scottlawsonbc/FilamentDiameterSensor/code/EdgeFinder/coordinate-reference.png

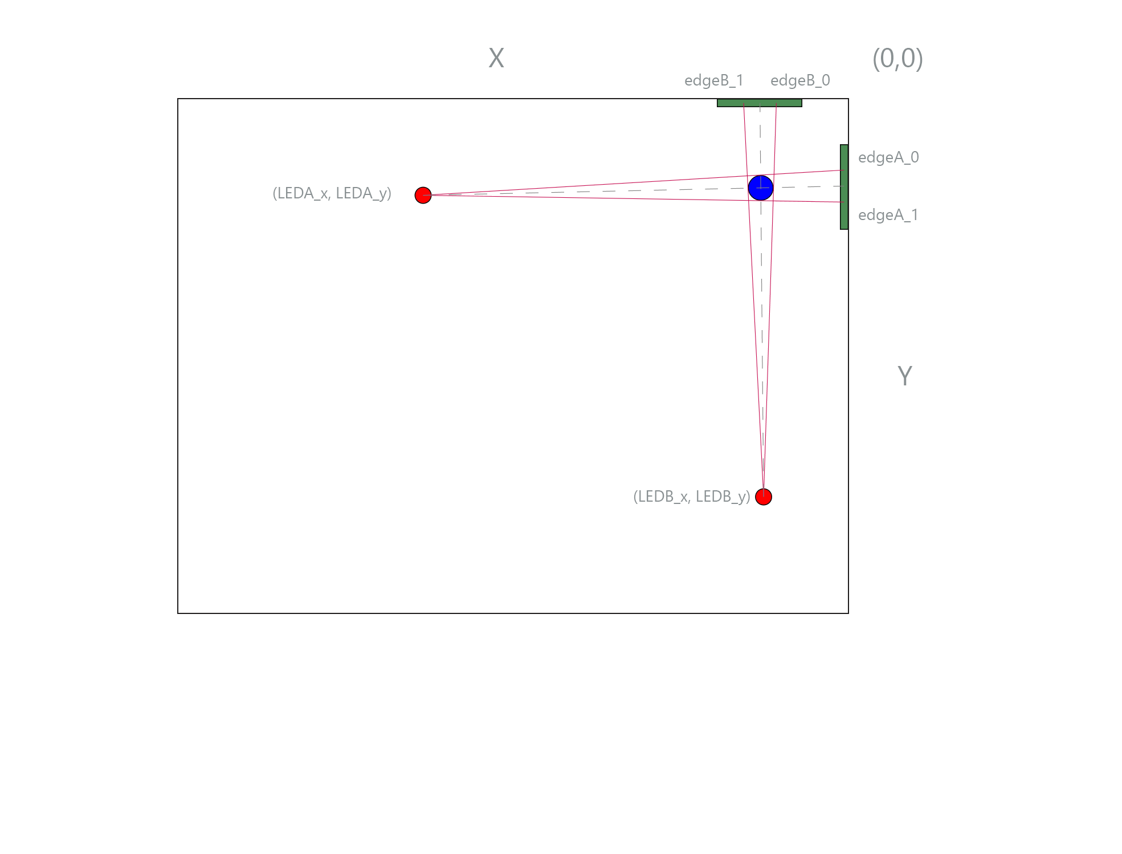
code/EdgeFinder/coordinate-reference.png
