scottlawsonbc/FilamentDiameterSensor/pictures/simulator.png

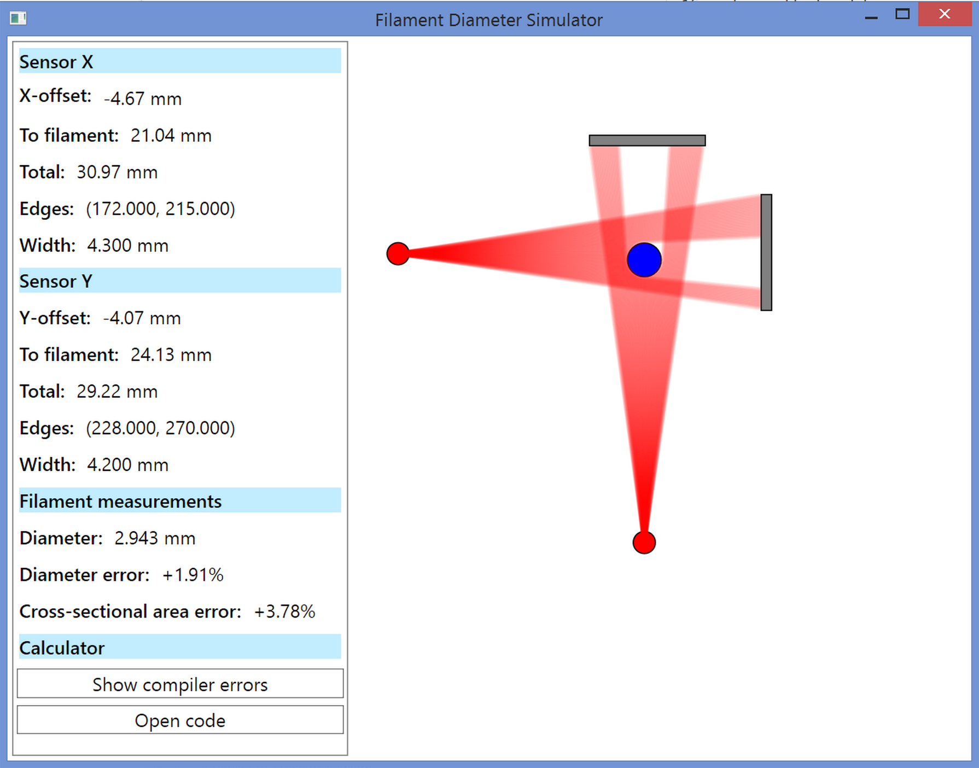
pictures/simulator.png
