scottlawsonbc/FilamentDiameterSensor/pictures/under-extrusion-example.jpg

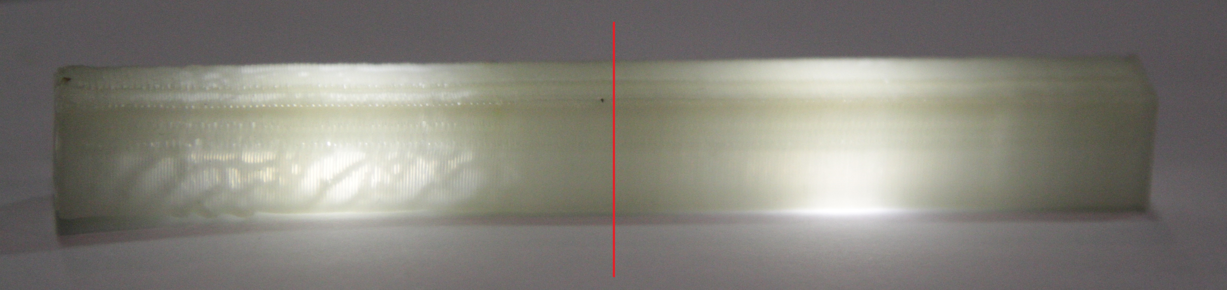
pictures/under-extrusion-example.jpg
