scottlawsonbc/FilamentDiameterSensor/reference-documents/stm32f3/adc-block-diagram.png

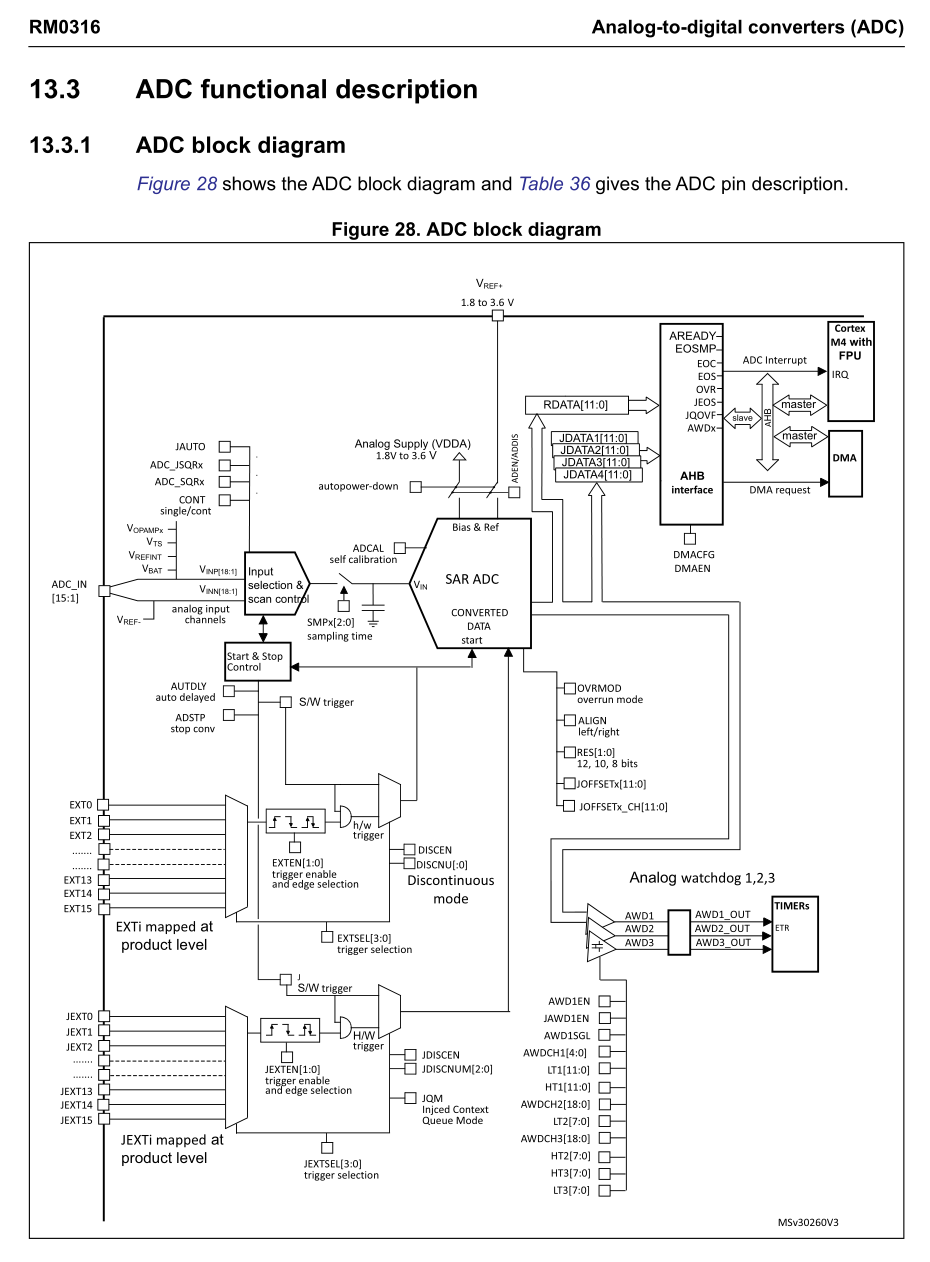
reference-documents/stm32f3/adc-block-diagram.png
