scottlawsonbc/FilamentDiameterSensor/reference-documents/stm32f3/adc-channel-mapping.png

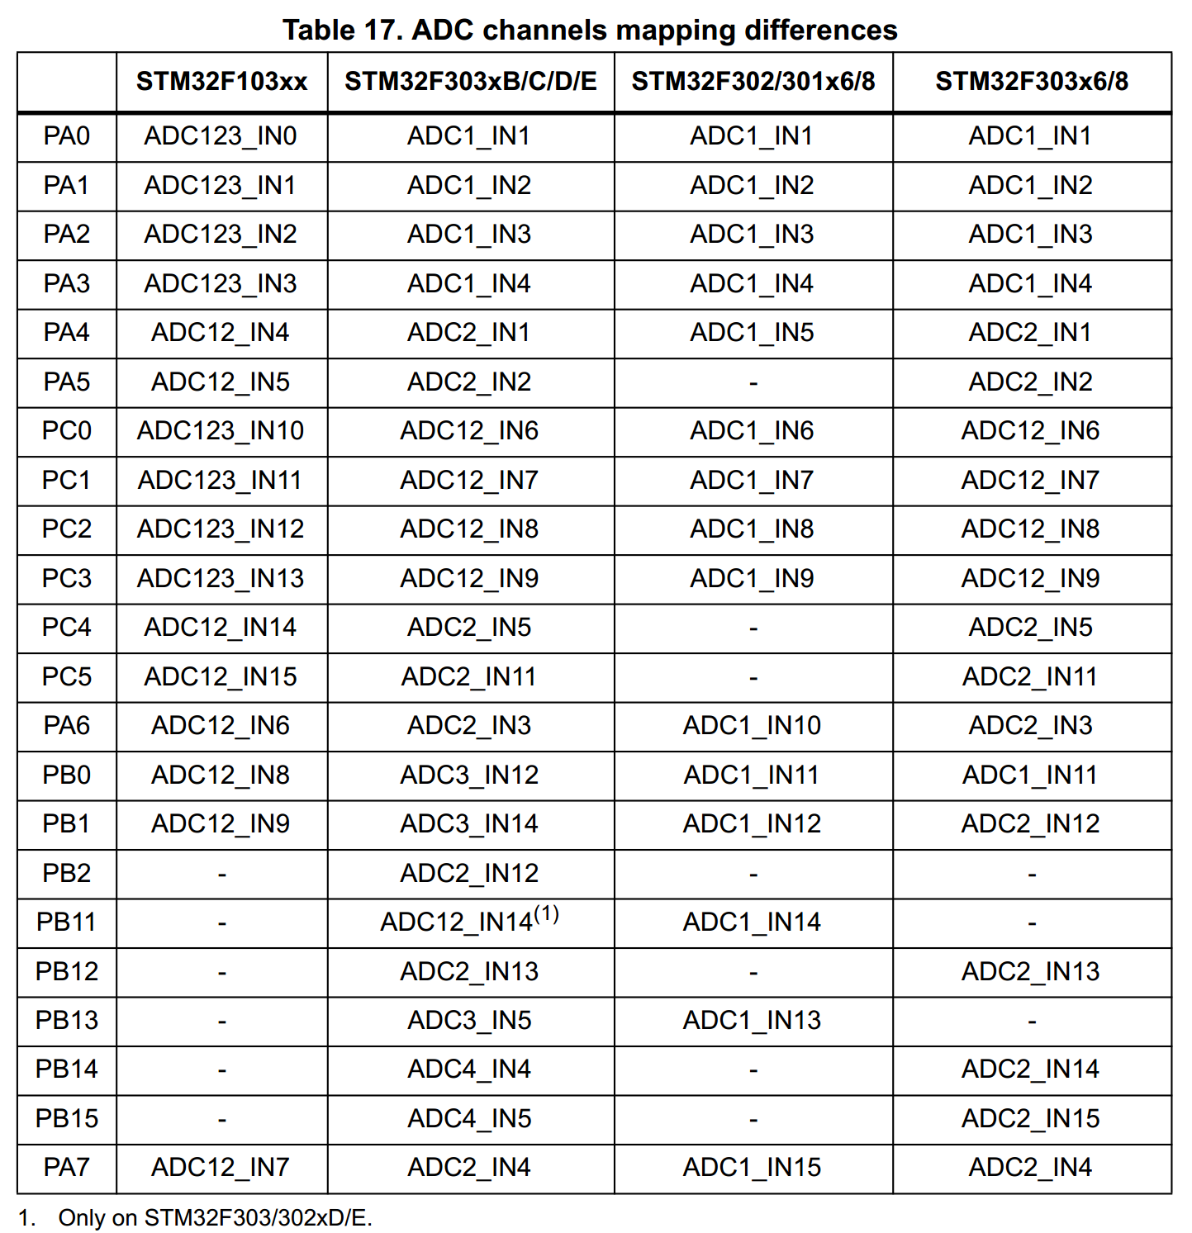
reference-documents/stm32f3/adc-channel-mapping.png
