scottlawsonbc/FilamentDiameterSensor/reference-documents/stm32f3/adc-channels-2.png

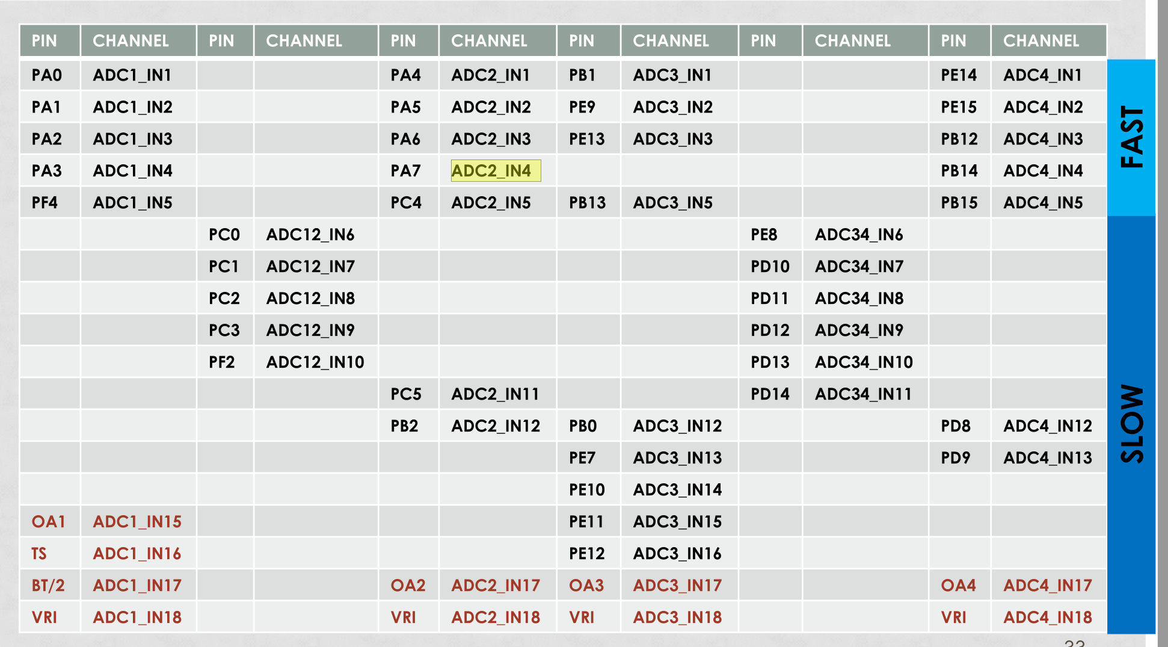
reference-documents/stm32f3/adc-channels-2.png
