scottlawsonbc/FilamentDiameterSensor/reference-documents/stm32f3/adc-channels.png

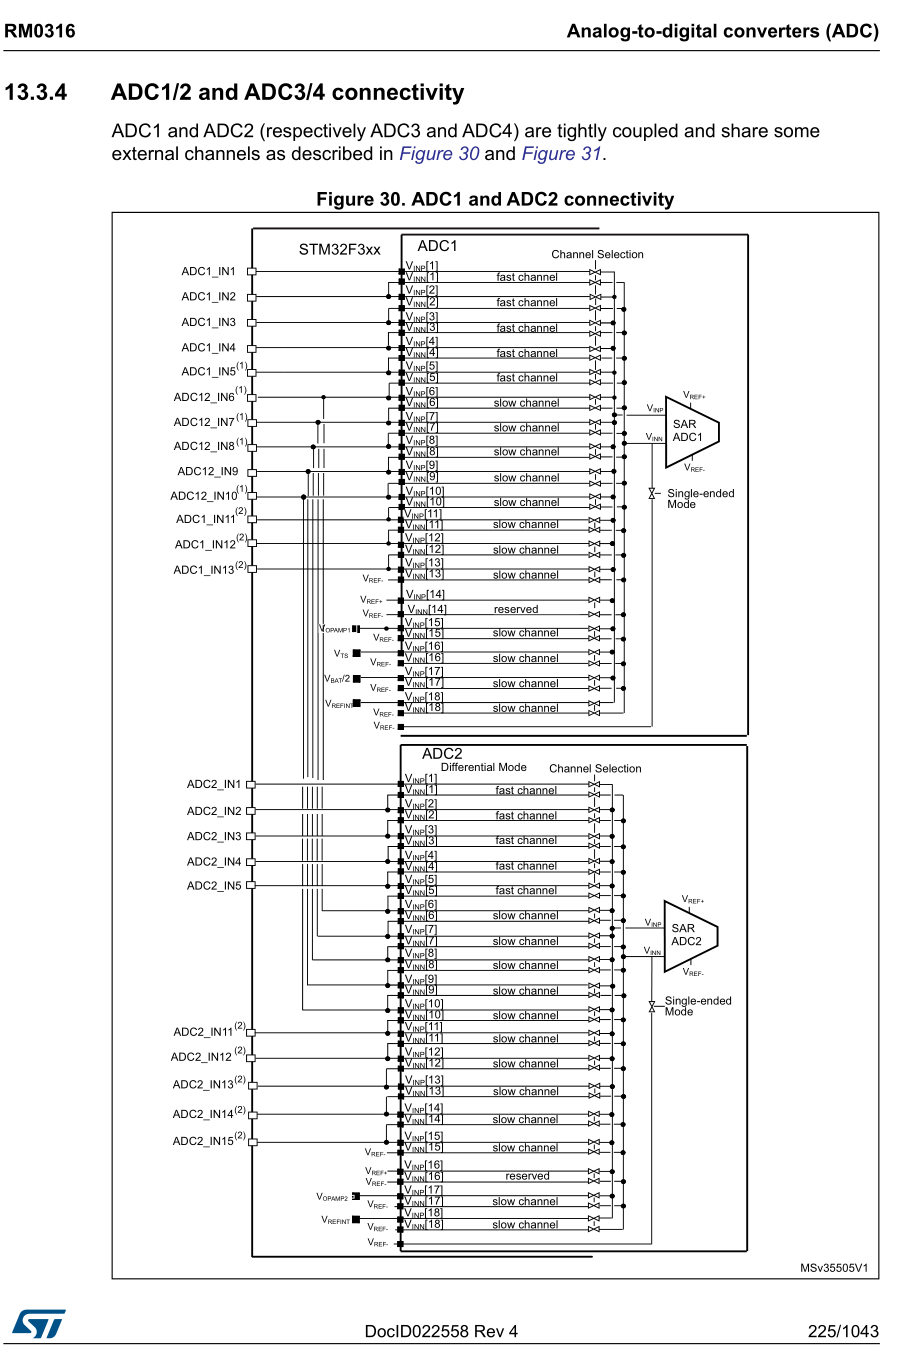
reference-documents/stm32f3/adc-channels.png
