scottlawsonbc/FilamentDiameterSensor/reference-documents/two-axis-sensor/pin-1.jpg

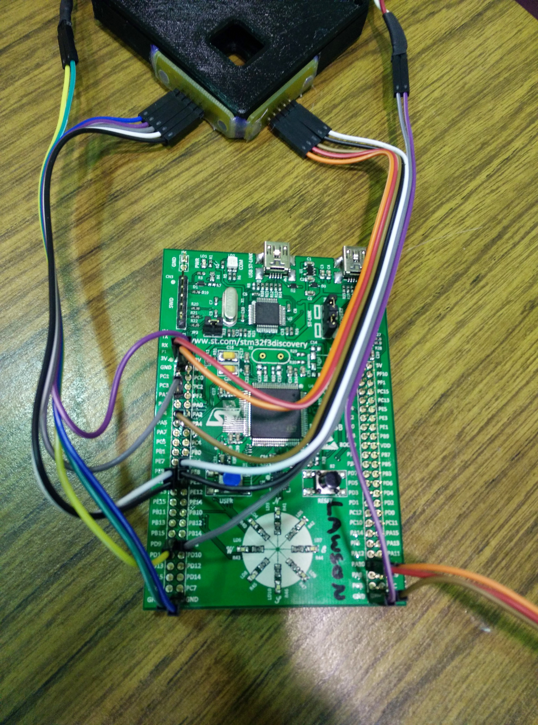
reference-documents/two-axis-sensor/pin-1.jpg
