scottlawsonbc/FilamentDiameterSensor/reference-documents/two-axis-sensor/pin-2.jpg

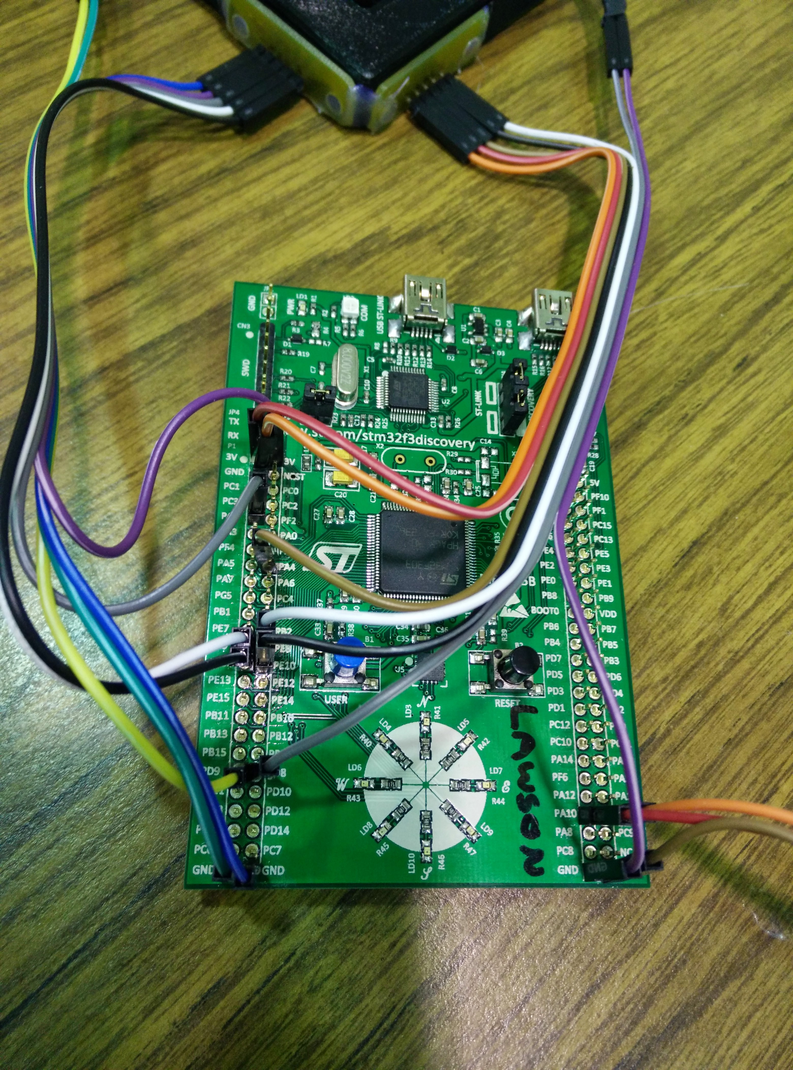
reference-documents/two-axis-sensor/pin-2.jpg
