scottlawsonbc/FilamentDiameterSensor/reference-documents/two-axis-sensor/pin-3.jpg

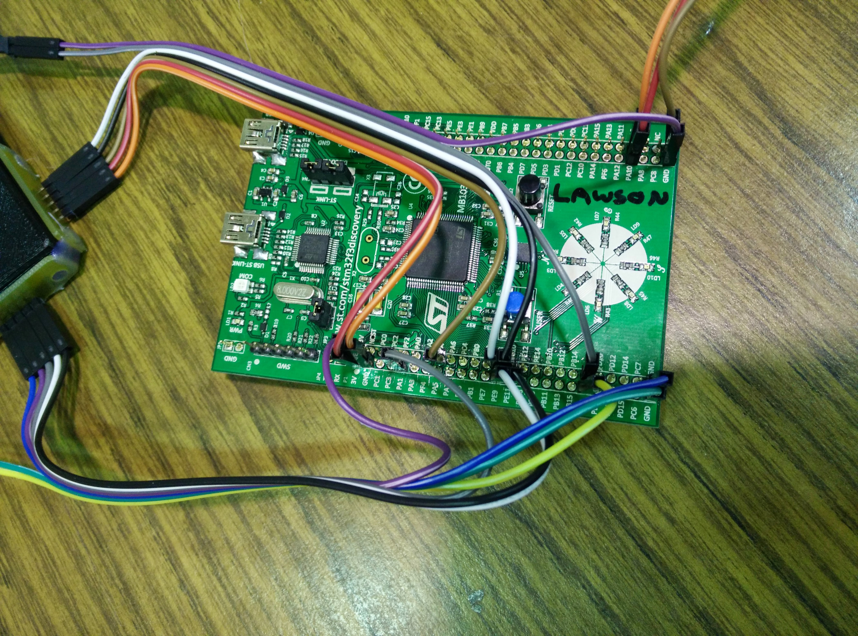
reference-documents/two-axis-sensor/pin-3.jpg
