scottlawsonbc/FilamentDiameterSensor/solidworks/printer-adapted-sensor/printer-adapted-chassis.SLDPRT

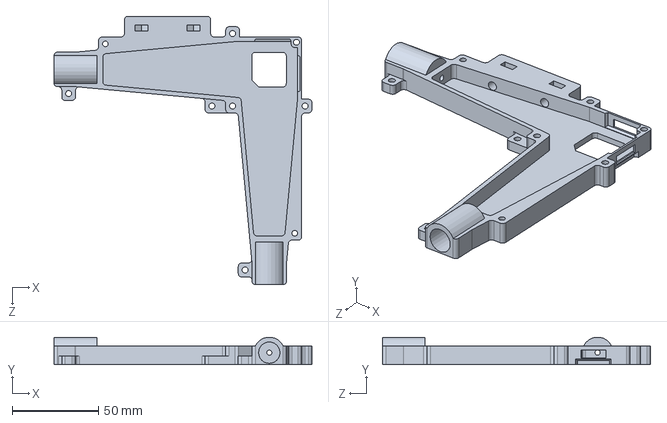
[picture p37: CAD file, 2015-03-22]
solidworks/printer-adapted-sensor/printer-adapted-chassis.SLDPRT
149.5 x 15.9 x 155.5 mm
