scottlawsonbc/FilamentDiameterSensor/solidworks/2-axis-prototype/Lid Insert Var1.STL

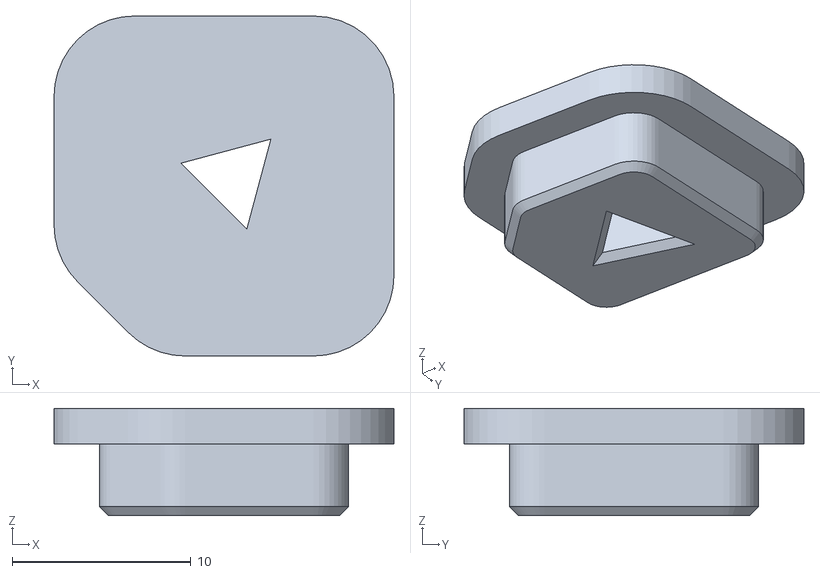
[picture p38: CAD file, 2015-02-26]
solidworks/2-axis-prototype/Lid Insert Var1.STL
19.0 x 19.0 x 6.00
