scottlawsonbc/FilamentDiameterSensor/code/sensor/sensor/source/geometry.c

#include <stdint.h>
#include <stdlib.h>
#include <math.h>
#include "edge-detection.h"
#include "tsl1401cl.h"
#include "geometry.h"
#include "usart.h"
#include "stdio.h"

/* Adds offset based on TSL1401 sensor placements in 2-axis sensor
*/
void GEO_Add_Sensor_Offsets(EdgeData* edge_position_a, EdgeData* edge_position_b)
{
	float sensor_edge_to_first_pixel_mm = TSL_EDGE_TO_FIRST_PIXEL_NM / 1000.f / 1000.f;
	edge_position_a->E0 += GEO_A_SENSOR_OFFSET_MM + sensor_edge_to_first_pixel_mm;
	edge_position_a->E1 += GEO_A_SENSOR_OFFSET_MM + sensor_edge_to_first_pixel_mm;
	edge_position_b->E0 =  GEO_B_SENSOR_OFFSET_MM - sensor_edge_to_first_pixel_mm - edge_position_b->E0; /* Referenced from far end of sensor */
	edge_position_b->E1 =  GEO_B_SENSOR_OFFSET_MM - sensor_edge_to_first_pixel_mm - edge_position_b->E1; /* Referenced from far end of sensor */
}

/* Returns an averaged diameter based on the two perpendicular widths
*/
inline float GEO_Averaged_Diameter(float diameter_A, float diameter_B)
{
	//return sqrt(diameter_A * diameter_B); /* geometric mean */
	return (diameter_A + diameter_B)/2.0f; /* arithmetic mean */
}

/* Returns the filament diameter
*/
float GEO_Filament_Diameter_MM(EdgeData edge_position_a, EdgeData edge_position_b)
{
	uprintf("Edges w/o offset:\r\nX: E0: %fmm E1: %fmm\r\nY: E0: %fmm E1: %fmm\r\n", edge_position_a.E0, edge_position_a.E1, edge_position_b.E0, edge_position_b.E1);

	GEO_Add_Sensor_Offsets(&edge_position_a, &edge_position_b);
	
	uprintf("Edges w/offset:\r\nX: E0: %fmm E1: %fmm\r\nY: E0: %fmm E1: %fmm\r\n", edge_position_a.E0, edge_position_a.E1, edge_position_b.E0, edge_position_b.E1);
	
	float x_a1 = edge_position_a.E1 - GEO_A_LED_Y_MM;
	float x_a0 = edge_position_a.E0 - GEO_A_LED_Y_MM;
	float x_b1 = edge_position_b.E0 - GEO_B_LED_X_MM;
	float x_b0 = edge_position_b.E1 - GEO_B_LED_X_MM;

	float X_a = (x_a1 + x_a0 == 0) ? 0 : GEO_A_LED_X_MM * tanf(0.5 * (atan2(x_a1, GEO_A_LED_X_MM) + atan2f(x_a0, GEO_A_LED_X_MM)));
	float X_b = (x_b1 + x_b0 == 0) ? 0 : GEO_B_LED_Y_MM * tanf(0.5 * (atan2(x_b1, GEO_B_LED_Y_MM) + atan2f(x_b0, GEO_B_LED_Y_MM)));

	float P_a = X_a + GEO_A_LED_Y_MM;
	float P_b = X_b + GEO_B_LED_X_MM;
			
	float fil_x = (GEO_A_LED_X_MM * (fmaf(GEO_B_LED_X_MM, P_a, fmaf(-P_a, P_b, GEO_B_LED_Y_MM * P_b)))) / (GEO_A_LED_X_MM * GEO_B_LED_Y_MM + fmaf(-P_a, P_b, -GEO_A_LED_Y_MM * GEO_B_LED_X_MM) + fmaf(GEO_A_LED_Y_MM, P_b, GEO_B_LED_X_MM * P_a));
	float fil_y = (GEO_B_LED_Y_MM * (fmaf(GEO_A_LED_X_MM, P_a, fmaf(-P_a, P_b, GEO_A_LED_Y_MM * P_b)))) / (GEO_A_LED_X_MM * GEO_B_LED_Y_MM + fmaf(-P_a, P_b, -GEO_A_LED_Y_MM * GEO_B_LED_X_MM) + fmaf(GEO_A_LED_Y_MM, P_b, GEO_B_LED_X_MM * P_a));

	float dia_a = 2.0f * sqrtf((fil_y - GEO_A_LED_Y_MM) * (fil_y - GEO_A_LED_Y_MM) + (GEO_A_LED_X_MM - fil_x) * (GEO_A_LED_X_MM - fil_x)) * sinf((atan2f(x_a1, GEO_A_LED_X_MM) - atan2f(x_a0, GEO_A_LED_X_MM))/2.0f);
	float dia_b = 2.0f * sqrtf((fil_x - GEO_B_LED_X_MM) * (fil_x - GEO_B_LED_X_MM) + (GEO_B_LED_Y_MM - fil_y) * (GEO_B_LED_Y_MM - fil_y)) * sinf((atan2f(x_b1, GEO_B_LED_Y_MM) - atan2f(x_b0, GEO_B_LED_Y_MM))/2.0f);

	uprintf("Diameter A: %fmm Diameter B: %fmm\r\n", dia_a, dia_b);

	return GEO_Averaged_Diameter(dia_a, dia_b);
}
