scottlawsonbc/FilamentDiameterSensor/code/sensor/sensor/source/tsl1401cl.h

/*
* Module prefix: TSL
* Methods for interfacing with the TSL1401CL linear photodiode array.
*/
#ifndef TSL1401CL_H
#define TSL1401CL_H
#include <stdint.h>
#include <stm32f30x_gpio.h>
#include <stm32f30x_adc.h>
#include <stm32f30x.h>

/* Sensor parameters */
#define TSL_PIXEL_COUNT             (128U)
#define TSL_PIXEL_SPACING_NM        (63500U)
#define TSL_SENSOR_WIDTH_NM         (TSL_PIXEL_SPACING_NM*TSL_PIXEL_COUNT)
#define TSL_EDGE_TO_FIRST_PIXEL_NM	(716800U)

/* Timing parameters */
#define TSL_CHARGE_TRANSFER_TIME_US (20U)
#define TSL_SENSOR_DELAY_US         (TSL_CHARGE_TRANSFER_TIME_US + 10U)
#define TSL_CLOCK_DELAY_US          (0U)

/* Digital pins connected to GPIOE */
#define TSL_SERIAL_PIN              (GPIO_Pin_11 | GPIO_Pin_10) 
#define TSL_CLOCK_PIN               (GPIO_Pin_9  | GPIO_Pin_8)

/* ADC1 connected to GPIOA */
#define TSL_ADC1_INPUT_PIN          (GPIO_Pin_2)
#define TSL_ADC1_CHANNEL		    (ADC_Channel_3)
/* ADC2 connected to GPIOA */
#define TSL_ADC2_INPUT_PIN		    (GPIO_Pin_6)
#define TSL_ADC2_CHANNEL            (ADC_Channel_3)

extern void TSL_Init();
//extern void TSL_MeasurePixels(int32_t *pixels);
extern void TSL_MeasurePixels(int32_t *x_pixels, int32_t *y_pixels);

#endif
